flamwenco/cutiepie/Case Files/Plates/2x1.75u Plate.dxf

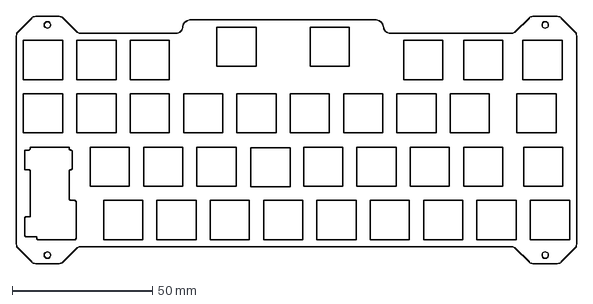
[picture p15: CAD file, 2023-02-27]
Case Files/Plates/2x1.75u Plate.dxf
200.0 x 88.2 mm
