flamwenco/cutiepie/Case Files/Symmetrical 4u 2x2u Case/symmetric_cutiepie_4u_plate.dxf

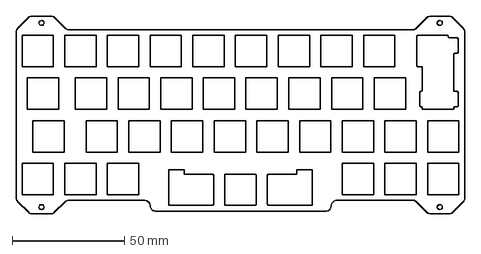
[picture p16: CAD file, 2023-07-15]
Case Files/Symmetrical 4u 2x2u Case/symmetric_cutiepie_4u_plate.dxf
200.0 x 88.2 mm
