flamwenco/cutiepie/Case Files/Plates/3u Plate.dxf

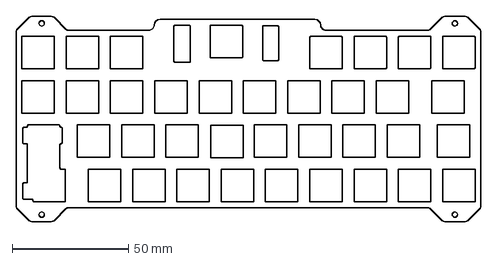
[picture p17: CAD file, 2023-02-27]
Case Files/Plates/3u Plate.dxf
200.0 x 88.2 mm
