flamwenco/cutiepie/Case Files/Plates/4u Plate.dxf

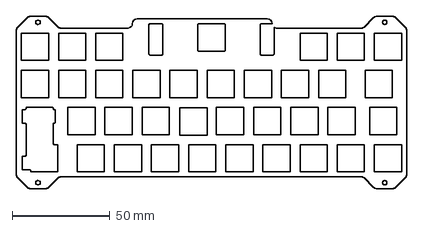
[picture p18: CAD file, 2023-02-27]
Case Files/Plates/4u Plate.dxf
200.0 x 88.2 mm
